jonaskello/wpc-cabinet/references/backbox_back_and_side_v1.png

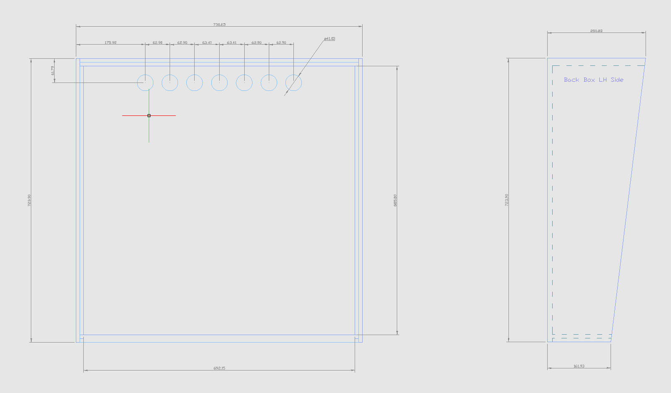
references/backbox_back_and_side_v1.png
