jonaskello/wpc-cabinet/references/cab_back_v1.png

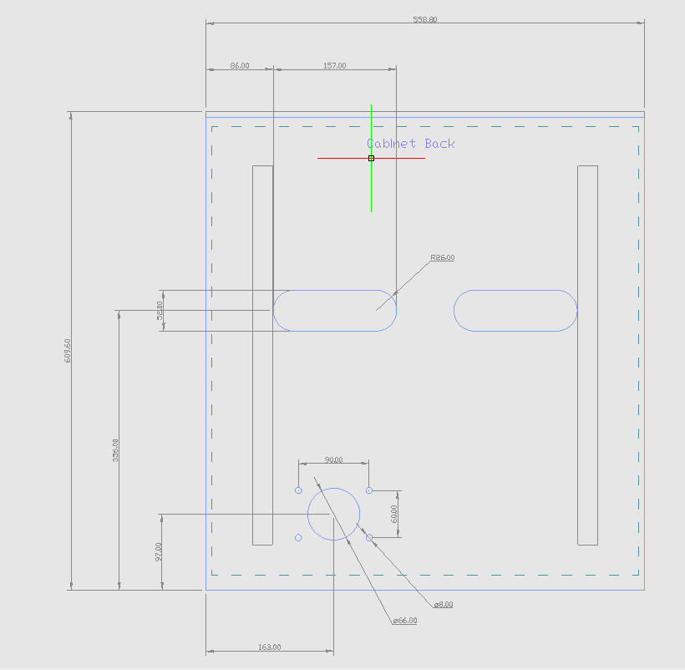
references/cab_back_v1.png
