jonaskello/wpc-cabinet/references/cab_front_v2.png

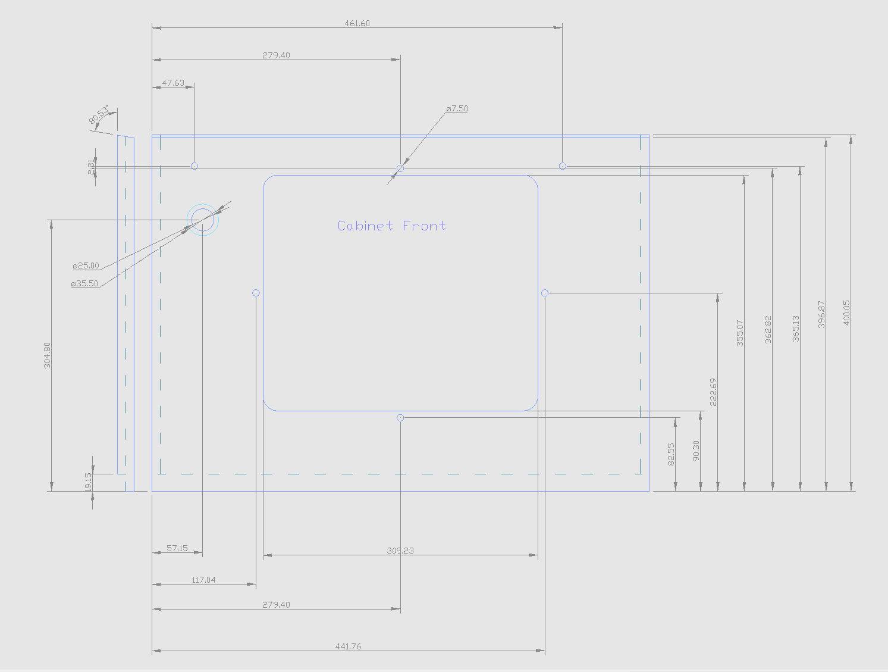
references/cab_front_v2.png
