jonaskello/wpc-cabinet/references/cab_top_zoom.png

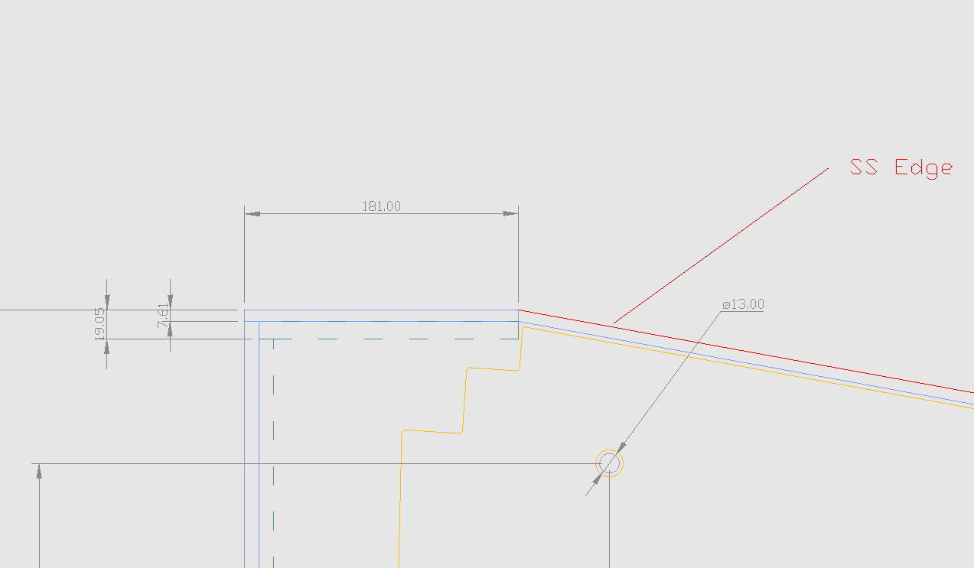
references/cab_top_zoom.png
