jonaskello/wpc-cabinet/references/cab_underside_v1.png

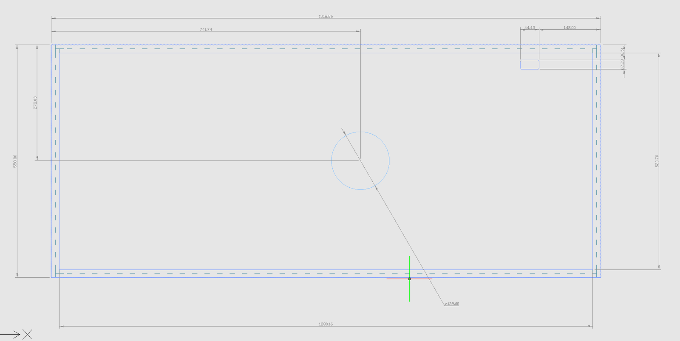
references/cab_underside_v1.png
