jonaskello/wpc-cabinet/references/coin_door.gif

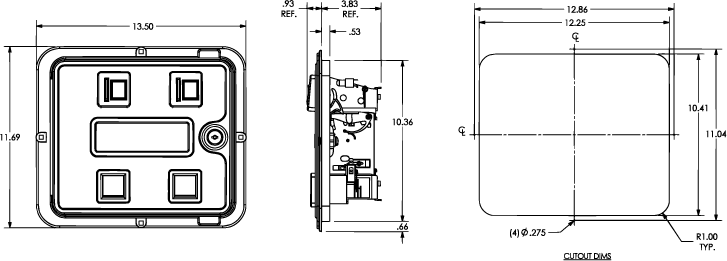
references/coin_door.gif
