jonaskello/wpc-cabinet/references/cab_assembly_v2.png

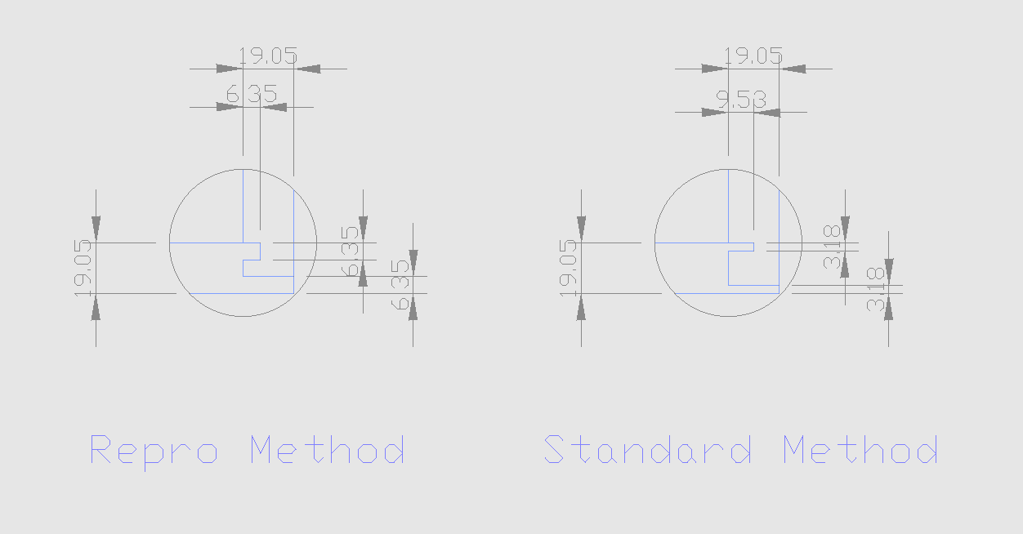
references/cab_assembly_v2.png
